Nu-hin/rhino/firmware/common.h

#ifndef COMMON_H_
#define COMMON_H_

#define clockCyclesPerMicrosecond() ( F_CPU / 1000000L )
#define clockCyclesToMicroseconds(a) ( (a) / clockCyclesPerMicrosecond() )
#define microsecondsToClockCycles(a) ( (a) * clockCyclesPerMicrosecond() )



#endif /* COMMON_H_ */
